yushen-qiu/Pervasive_Computing/01_Code/firmware/src/LED/LEDModule.cpp

// LED utilities for orientation/navigation display
#include <LED/LEDModule.h>
#include <math.h>
#include <sensors/Orientation.h>

static CRGB leds[Pins::LED_COUNT];
static bool triggered100m = false;
static bool triggered50m  = false;

// init
void initLED() {
    FastLED.addLeds<LED_TYPE, Pins::LED, COLOR_ORDER>(leds, Pins::LED_COUNT);
    FastLED.setBrightness(BRIGHTNESS);
    FastLED.clear();
    FastLED.show();
}

// Orientation LED display
static const int DIRECTION_MAP[16] = {
        0,  1,  15, 14, // N
        13, 12, 11, 10, // E
        9,  8,  7,  6,  // S
        5,  4,  3,  2   // W
};

void displayOrientationLED(const OrientationResult& o) {
    if (isnan(o.relativeAngle)) {
        Serial.println("[LED] Invalid orientation data.");
        return;
    }

    FastLED.clear();

    // Normalize to [-180, 180)
    double rel = fmod(o.relativeAngle + 540.0, 360.0) - 180.0;
    int    dir = -1;

    // Determine which direction to light
    if (rel >= -45 && rel < 45)
        dir = 0; // Forward (N)
    else if (rel >= 45 && rel < 135)
        dir = 1; // Right (E)
    else if (rel <= -45 && rel > -135)
        dir = 3; // Left (W)
    else
        dir = 2; // Back (S)

    // Select LED colour
    CRGB color = CRGB::Blue;

    // Light up LEDs according to DIRECTION_MAP
    int startIndex = dir * 4;
    for (int i = 0; i < 4; i++) {
        int ledIndex   = DIRECTION_MAP[startIndex + i];
        leds[ledIndex] = color;
    }

    FastLED.show();

    const char* dirName[] = {"Forward", "Right", "Back", "Left"};
    Serial.printf("[LED] Dir: %s | Rel=%.1f° | Head=%.1f° | Target=%.1f°\n", dirName[dir], rel,
                  o.currentHeading, o.targetBearing);
}

// 100 m: breathe in yellow
static void breatheYellow() {
    for (int cycle = 0; cycle < 5; cycle++) {
        for (int b = 0; b <= 255; b += 5) {
            fill_solid(leds, Pins::LED_COUNT, CRGB(b, b, 0)); // Yellow
            FastLED.show();
            delay(8);
        }
        for (int b = 255; b >= 0; b -= 5) {
            fill_solid(leds, Pins::LED_COUNT, CRGB(b, b, 0));
            FastLED.show();
            delay(8);
        }
    }
    FastLED.clear();
    FastLED.show();
}

void turnOffLED() {
    FastLED.clear();
    FastLED.show();
}

void showColorLED(int R, int G, int B) {
    fill_solid(leds, Pins::LED_COUNT, CRGB(R, G, B));
    FastLED.show();
}

// 50 m: rainbow effect for 20 seconds
static void rainbowEffect() {
    unsigned long start = millis();
    uint8_t       hue   = 0;
    while (millis() - start < 20000) {
        fill_rainbow(leds, Pins::LED_COUNT, hue++, 7);
        FastLED.show();
        delay(30);
    }
    FastLED.clear();
    FastLED.show();
}

void handleNavigationLED(const NavigationData& nav) {
    // --- First time entering the 100 metres ---
    if (!triggered100m && nav.distanceMeters <= 100 && nav.distanceMeters > 50) {
        Serial.println("[NAV LED] Within 100 m → Yellow breathing");
        triggered100m = true;
        breatheYellow();
    }

    // --- First time entering 50 metres ---
    if (!triggered50m && nav.distanceMeters <= 50) {
        Serial.println("[NAV LED] Within 50 m → Rainbow then shutdown");
        triggered50m = true;
        rainbowEffect();

        // Shut down the system
        ESP.restart();
    }
}
